jp112sdl/HB-SCI-x-MSP/Blender/472.png

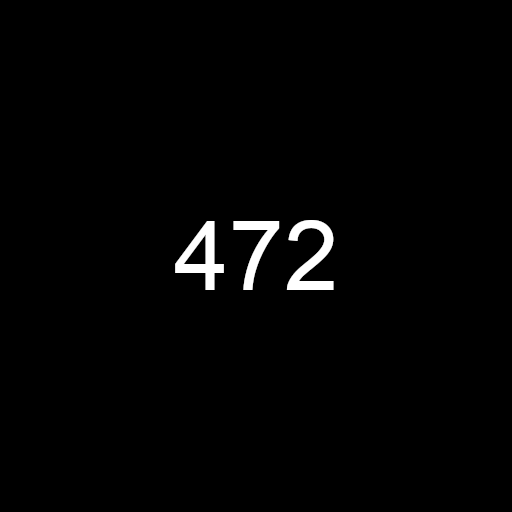
Blender/472.png
