jp112sdl/HB-SCI-x-MSP/Blender/32768.png

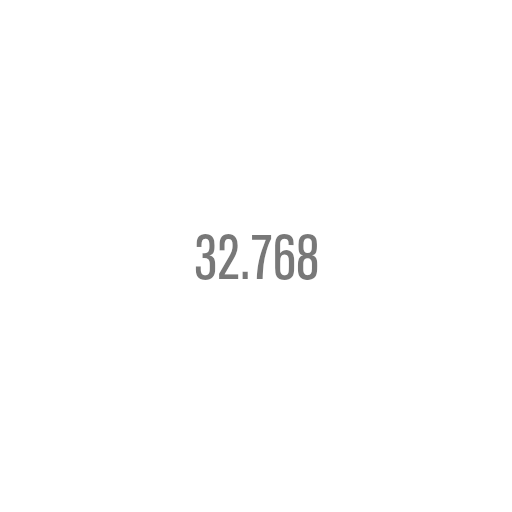
Blender/32768.png
