jp112sdl/HB-SCI-x-MSP/Blender/ATmega328P Ausschnitt.jpg

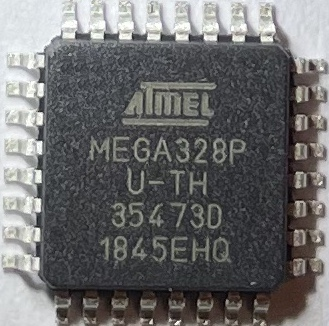
Blender/ATmega328P Ausschnitt.jpg
