jp112sdl/HB-SCI-x-MSP/Blender/CC1101_IC.jpg

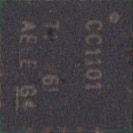
Blender/CC1101_IC.jpg
