jp112sdl/HB-SCI-x-MSP/Blender/CR2032.jpg

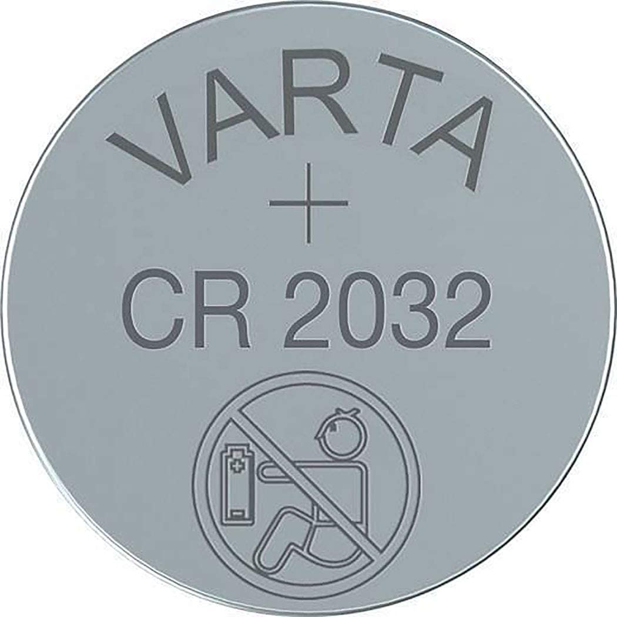
Blender/CR2032.jpg
