jp112sdl/HB-SCI-x-MSP/Blender/MSP430F2001.jpg

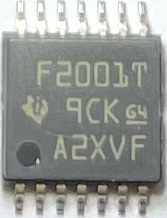
Blender/MSP430F2001.jpg
