jp112sdl/HB-SCI-x-MSP/PCB/3DFront.png

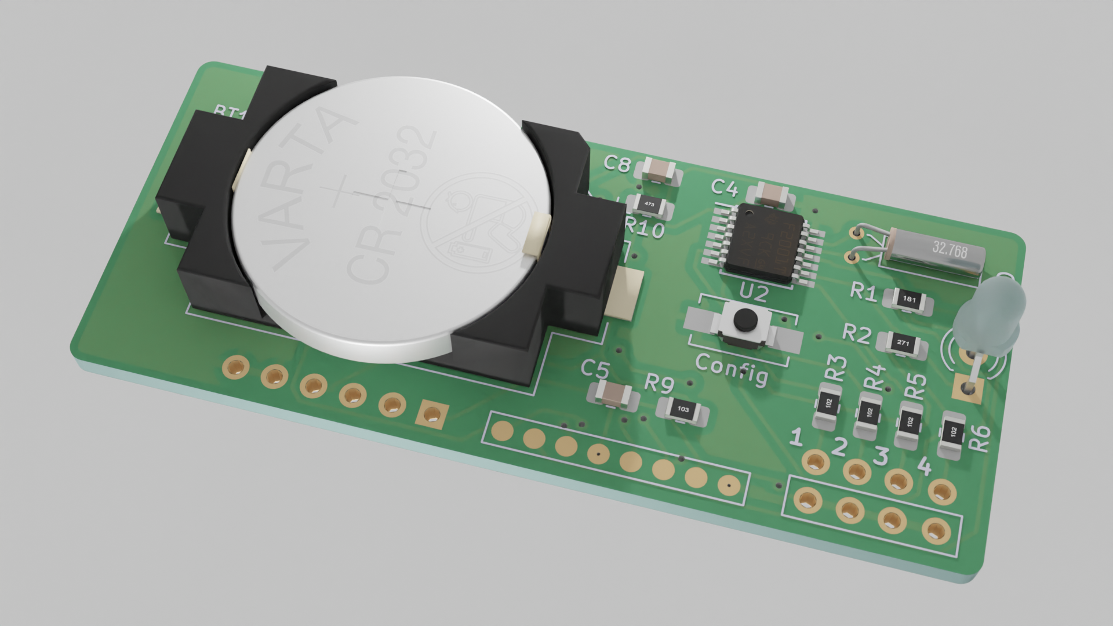
PCB/3DFront.png
